ikorb/tapecart/src-c64/tcrt.c

/* tapecart - a tape port storage pod for the C64

   Copyright (C) 2013-2022  Ingo Korb <ingo@akana.de>
   All rights reserved.
   Idea by enthusi

   Redistribution and use in source and binary forms, with or without
   modification, are permitted provided that the following conditions
   are met:
   1. Redistributions of source code must retain the above copyright
      notice, this list of conditions and the following disclaimer.
   2. Redistributions in binary form must reproduce the above copyright
      notice, this list of conditions and the following disclaimer in the
      documentation and/or other materials provided with the distribution.

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

   tcrt.c: TCRT read/write

*/

#include <conio.h>
#include <stdio.h>
#include <string.h>
#include "conutil.h"
#include "fileselector.h"
#include "globals.h"
#include "io.h"
#include "tapecartif.h"
#include "utils.h"
#include "tcrt.h"

const uint8_t tcrt_header[] = {
  0x74, 0x61, 0x70, 0x65,
  0x63, 0x61, 0x72, 0x74,
  0x49, 0x6d, 0x61, 0x67,
  0x65, 0x0d, 0x0a, 0x1a
};

static struct {
  uint16_t dataofs;
  uint16_t datalen;
  uint16_t calladdr;
} loadinfo;

static uint32_t tcrt_flashsize;

void write_tcrt(void) {
  current_function = "Write TCRT";
  update_top_status();
  select_file();
  if (!fname[0])
    return;

  start_timing();

  res = tc_cbm_open(fname);
  if (res != 0) {
    cputsxy(2, STATUS_START - 2, "Failed to open file");
    return;
  }

  bytesread = tc_cbm_read(databuffer, TCRT_OFFSET_FLASHDATA);
  if (bytesread != TCRT_OFFSET_FLASHDATA) {
    gotoxy(2, STATUS_START - 2);
    cprintf("Error: Read only %d byte from the file", len);
    goto fail;
  }

  /* sanity-check TCRT data fields */
  if (memcmp(databuffer, tcrt_header, TCRT_HEADER_SIZE)) {
    cputsxy(2, STATUS_START - 2, "Error: File header not recognized");
    goto fail;
  }

  if (databuffer[TCRT_OFFSET_VERSION] != TCRT_VERSION ||
      databuffer[TCRT_OFFSET_VERSION + 1] != 0) {
    cputsxy(2, STATUS_START - 2, "Error: File uses unknown TCRT version");
    goto fail;
  }

  memcpy(&tcrt_flashsize, databuffer + TCRT_OFFSET_FLASHLENGTH, 4);
  if (tcrt_flashsize > total_size) {
    cputsxy(2, STATUS_START - 2, "Error: TCRT flash size exceeds cartridge size");
    goto fail;
  }

  /* copy loader into place if not present */
  if (!(databuffer[TCRT_OFFSET_FLAGS] & TCRT_FLAG_LOADERPRESENT))
    memcpy(databuffer + TCRT_OFFSET_LOADER, default_loader, LOADER_LENGTH);

  /* avoid writing loader if it's identical to the one already in cart */
  tapecart_read_loader(databuffer + TCRT_OFFSET_FLASHDATA);
  if (memcmp(databuffer + TCRT_OFFSET_LOADER,
             databuffer + TCRT_OFFSET_FLASHDATA, LOADER_LENGTH)) {
    tapecart_write_loader(databuffer + TCRT_OFFSET_LOADER);
  }

  memcpy(&loadinfo, databuffer + TCRT_OFFSET_DATAADDR, sizeof(loadinfo));
  tapecart_write_loadinfo(loadinfo.dataofs,
                          loadinfo.datalen,
                          loadinfo.calladdr,
                          databuffer + TCRT_OFFSET_FILENAME);

  flash_offset = 0;
  flash_page   = 0;
  pages_erased = 0;

  if (!write_file(tcrt_flashsize)) {
    cputsxy(2, STATUS_START - 2, "Error: TCRT seems to be truncated");
    goto fail;
  }

  // FIXME: Check for EOF here to find out if TCRT is too long

  /* erase remaining space in cart */
  if (erase_pages) {
    /* page-erase cart */
    flash_offset += page_size - (flash_offset % page_size); // round up to start of next page
    flash_offset += page_size * pages_erased;
    while (flash_offset < total_size) {
      gotoxy(0, 9);
      cprintf("Erasing page %d [$%06lx]", flash_page, flash_offset);

      tapecart_erase_flashblock(flash_offset);

      flash_offset += page_size * erase_pages;
      flash_page   += erase_pages;
    }

  } else {
    /* byte-writeable cart */
    memset(databuffer, 0xff, sizeof(databuffer));
    while (flash_offset < total_size) {
      /* note: bytesread is a convenient, though misnamed 32-bit var here */
      bytesread = total_size - flash_offset;
      if (bytesread > sizeof(databuffer))
        bytesread = sizeof(databuffer);

      gotoxy(0, 9);
      cprintf("Erasing offset $%06lx", flash_offset);

      tapecart_write_flash(flash_offset, bytesread, databuffer);
      flash_offset += bytesread;
    }
  }

  cputsxy(2, STATUS_START - 2, "Write completed in ");
  print_timing();

 fail:
  tc_cbm_close();
}


void dump_tcrt(void) {
  memset(fname, 0, FILENAME_BUFFER_LENGTH);

  current_function = "Dump cart to TCRT";
  update_top_status();

  cputsxy(0, 10, "Note: Screen will be blanked,");
  cputsxy(6, 11, "hold RUN/STOP to abort.");

  //             0123456789012345678901234567890123456789
  cputsxy(0, 3, "File name: [                           ]");
  if (!read_string(fname, FILENAME_BUFFER_LENGTH - 1, 12, 3, 39 - 12))
    return;

  res = cbm_open(CBM_LFN, CURRENT_DEVICE, 1, fname);
  if (res != 0) {
    cputsxy(2, STATUS_START - 2, "Failed to open file");
    return;
  }

  memset(databuffer, 0, sizeof(databuffer));
  memcpy(databuffer, tcrt_header, TCRT_HEADER_SIZE);
  databuffer[TCRT_HEADER_SIZE] = TCRT_VERSION;

  tapecart_read_loadinfo(&loadinfo.dataofs,
                         &loadinfo.datalen,
                         &loadinfo.calladdr,
                         fname);
  memcpy(databuffer + TCRT_OFFSET_DATAADDR, &loadinfo, sizeof(loadinfo));
  memcpy(databuffer + TCRT_OFFSET_FILENAME, fname, FILENAME_LENGTH);

  databuffer[TCRT_OFFSET_FLAGS] = TCRT_FLAG_LOADERPRESENT;
  tapecart_read_loader(databuffer + TCRT_OFFSET_LOADER);

  memcpy(databuffer + TCRT_OFFSET_FLASHLENGTH, &total_size, sizeof(total_size));

  byteswritten = cbm_write(CBM_LFN, databuffer, TCRT_OFFSET_FLASHDATA);
  if (byteswritten != TCRT_OFFSET_FLASHDATA) {
    cputsxy(2, STATUS_START - 2, "Failed to write to file");
    cbm_close(CBM_LFN);
    return;
  }

  dump_flash_to_file();
}
