ikorb/tapecart/src-firmware/crc32.c

/**
 * \file crc32.c
 * Functions and types for CRC checks.
 *
 * Generated on Tue Apr 19 23:28:09 2016,
 * by pycrc v0.9, https://pycrc.org
 * using the configuration:
 *    Width         = 32
 *    Poly          = 0x04c11db7
 *    Xor_In        = 0xffffffff
 *    ReflectIn     = True
 *    Xor_Out       = 0xffffffff
 *    ReflectOut    = True
 *    Algorithm     = bit-by-bit-fast
 *****************************************************************************/
#include "crc32.h"     /* include the header file generated with pycrc */
#include <stdlib.h>
#include <stdint.h>
#include <stdbool.h>

/**
 * Reflect all bits of a \a data word of \a data_len bytes.
 *
 * \param data         The data word to be reflected.
 * \param data_len     The width of \a data expressed in number of bits.
 * \return             The reflected data.
 *****************************************************************************/
crc_t crc_reflect(crc_t data, size_t data_len)
{
    unsigned int i;
    crc_t ret;

    ret = data & 0x01;
    for (i = 1; i < data_len; i++) {
        data >>= 1;
        ret = (ret << 1) | (data & 0x01);
    }
    return ret;
}


/**
 * Update the crc value with new data.
 *
 * \param crc      The current crc value.
 * \param data     Pointer to a buffer of \a data_len bytes.
 * \param data_len Number of bytes in the \a data buffer.
 * \return         The updated crc value.
 *****************************************************************************/
crc_t crc_update(crc_t crc, const void *data, size_t data_len)
{
    const unsigned char *d = (const unsigned char *)data;
    unsigned int i;
    bool bit;
    unsigned char c;

    while (data_len--) {
        c = *d++;
        for (i = 0x01; i & 0xff; i <<= 1) {
            bit = crc & 0x80000000;
            if (c & i) {
                bit = !bit;
            }
            crc <<= 1;
            if (bit) {
                crc ^= 0x04c11db7;
            }
        }
        crc &= 0xffffffff;
    }
    return crc & 0xffffffff;
}
